ale-giustina/PCR_Thermocycler/build_photos/build_image_1.jpg

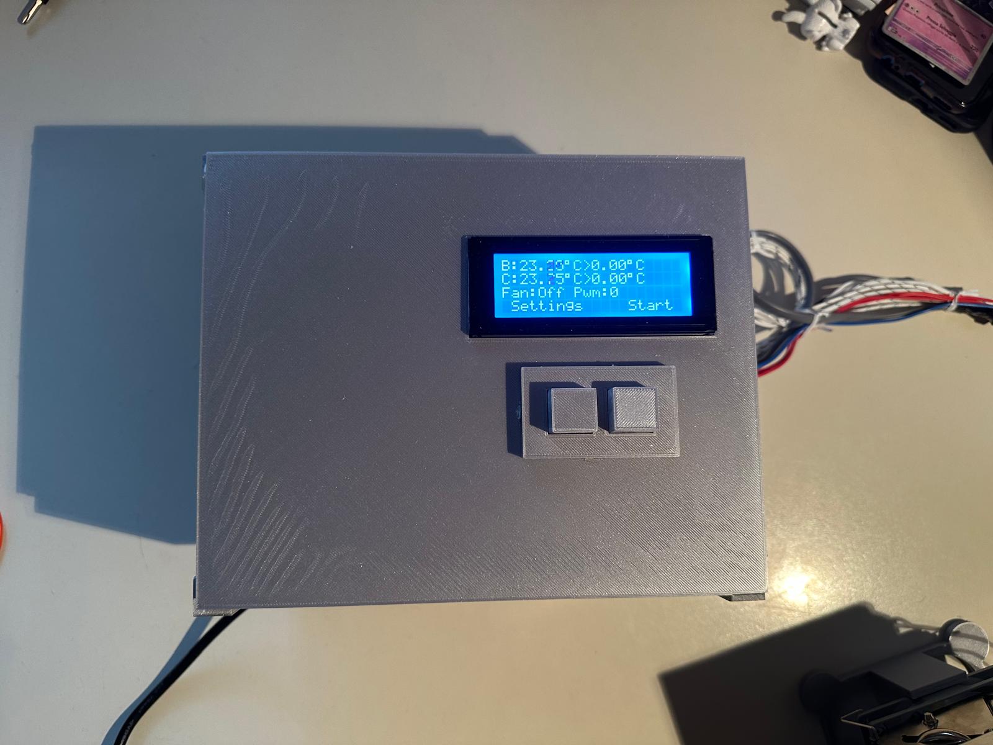
build_photos/build_image_1.jpg
