ale-giustina/PCR_Thermocycler/build_photos/build_image_2.jpg

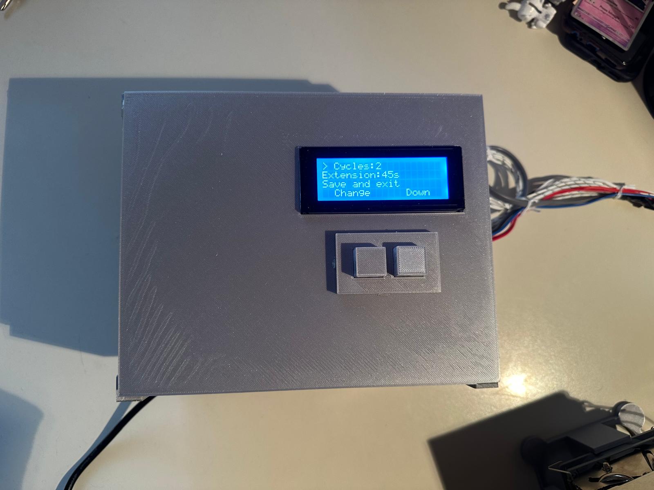
build_photos/build_image_2.jpg
