ale-giustina/PCR_Thermocycler/build_photos/build_image_3.jpg

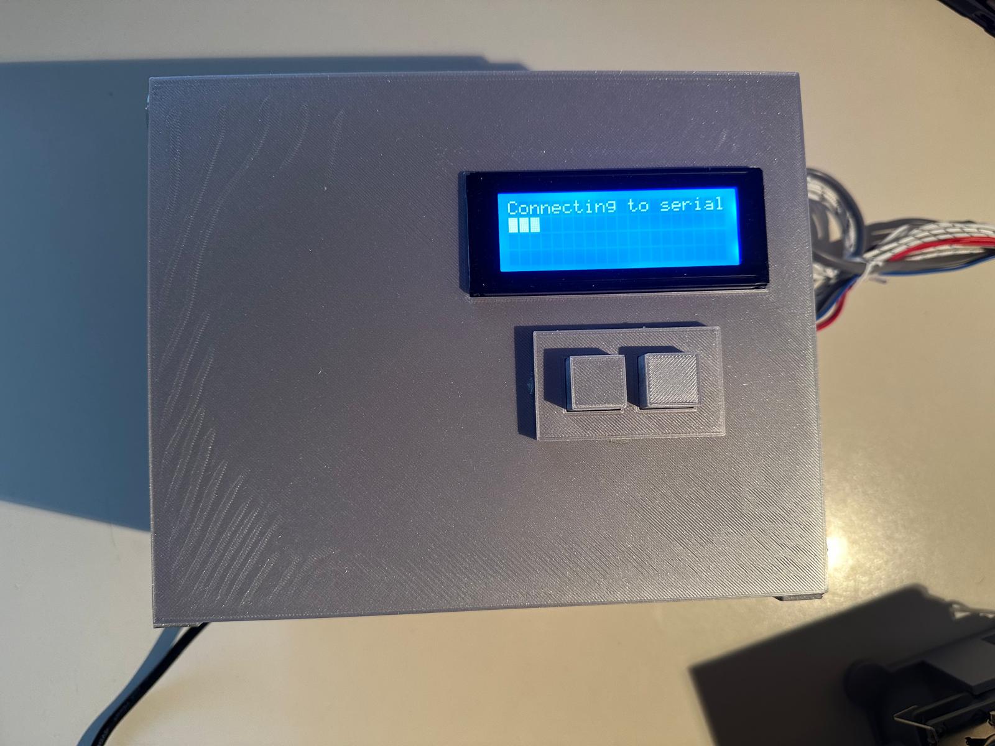
build_photos/build_image_3.jpg
