ale-giustina/PCR_Thermocycler/build_photos/build_image_9.jpg

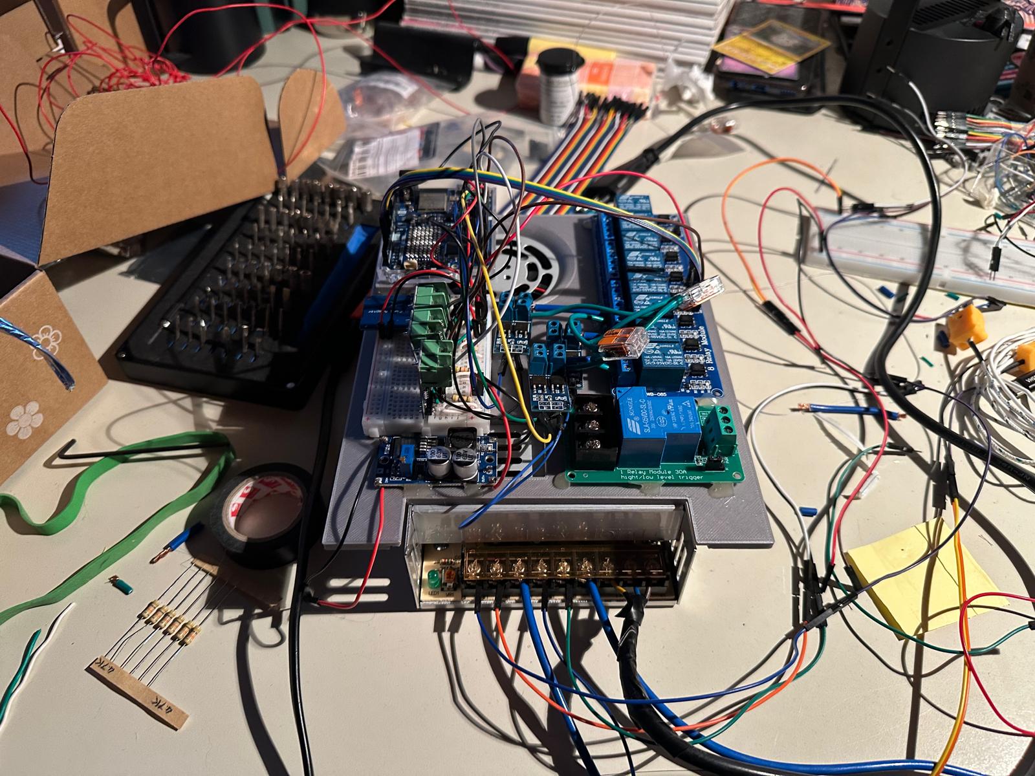
build_photos/build_image_9.jpg
