ale-giustina/PCR_Thermocycler/images/test_run.png

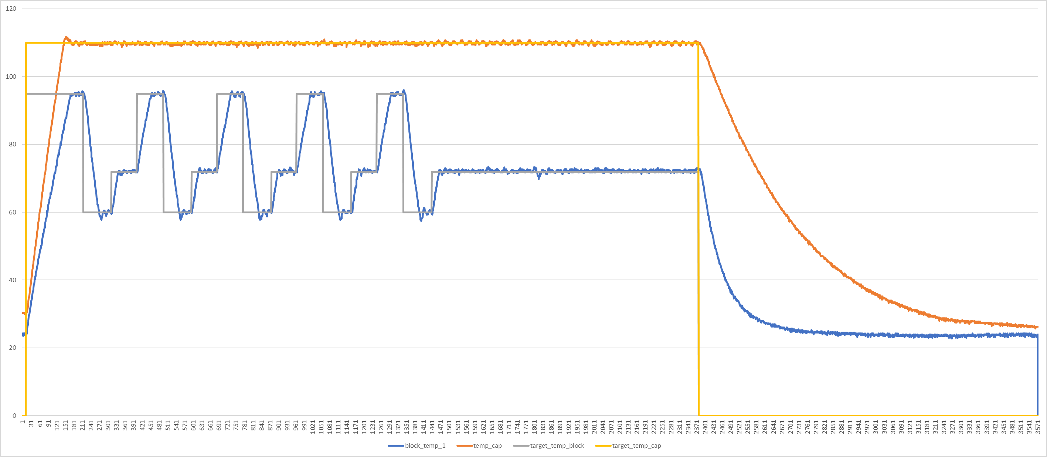
images/test_run.png
